CRM-UAM/CRMaze/Laberinto_OSHWDem/2016-10-10 19.41.19.jpg

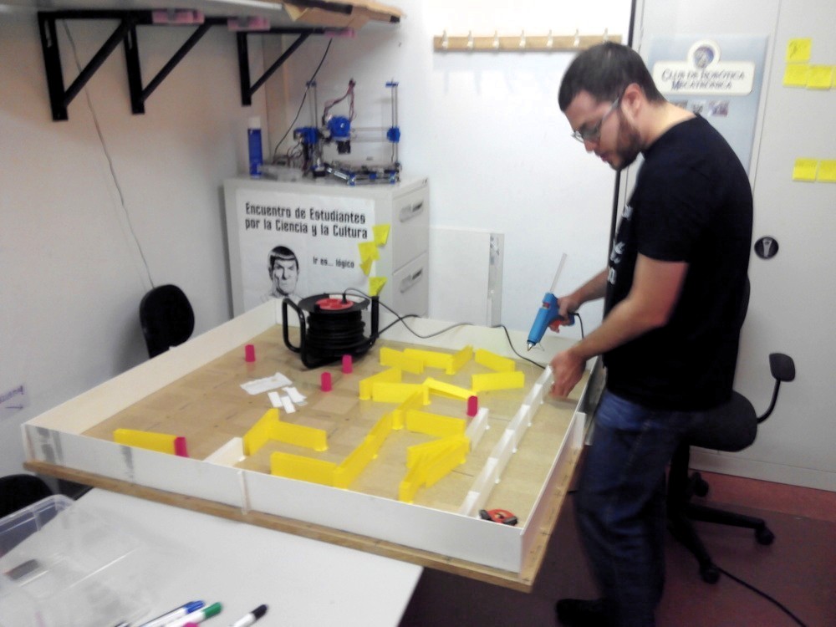
Laberinto_OSHWDem/2016-10-10 19.41.19.jpg
