CRM-UAM/CRMaze/Software/avr_lib_mpu6050_03/imu_arduino/imu_arduino.ino

#include <stdlib.h>
#include <avr/io.h>
#include <avr/interrupt.h>
#include <avr/pgmspace.h>
#include <util/delay.h>
#include <math.h>  //include libm

#include "mpu6050.h"

#define UART_BAUD_RATE 115200
#include "myuart.h"

int main(void) {

	#if MPU6050_GETATTITUDE == 0
    int16_t ax = 0;
    int16_t ay = 0;
    int16_t az = 0;
    int16_t gx = 0;
    int16_t gy = 0;
    int16_t gz = 0;
    double axg = 0;
    double ayg = 0;
    double azg = 0;
    double gxds = 0;
    double gyds = 0;
    double gzds = 0;
	#endif

	#if MPU6050_GETATTITUDE == 1 || MPU6050_GETATTITUDE == 2
    long *ptr = 0;
    double qw = 1.0f;
	double qx = 0.0f;
	double qy = 0.0f;
	double qz = 0.0f;
	double roll = 0.0f;
	double pitch = 0.0f;
	double yaw = 0.0f;
	#endif

    //init uart
	uart_init(UART_BAUD_SELECT(UART_BAUD_RATE,F_CPU));

	//init interrupt
	sei();

	//init mpu6050
	mpu6050_init();
	_delay_ms(50);

	//init mpu6050 dmp processor
	#if MPU6050_GETATTITUDE == 2
	mpu6050_dmpInitialize();
	mpu6050_dmpEnable();
	_delay_ms(10);
	#endif

	for(;;) {
		#if MPU6050_GETATTITUDE == 0
		mpu6050_getRawData(&ax, &ay, &az, &gx, &gy, &gz);
		mpu6050_getConvData(&axg, &ayg, &azg, &gxds, &gyds, &gzds);
		#endif

		#if MPU6050_GETATTITUDE == 1
		mpu6050_getQuaternion(&qw, &qx, &qy, &qz);
		mpu6050_getRollPitchYaw(&roll, &pitch, &yaw);
		_delay_ms(10);
		#endif

		#if MPU6050_GETATTITUDE == 2
		if(mpu6050_getQuaternionWait(&qw, &qx, &qy, &qz)) {
			mpu6050_getRollPitchYaw(qw, qx, qy, qz, &roll, &pitch, &yaw);
		}
		_delay_ms(10);
		#endif

		#if MPU6050_GETATTITUDE == 0
		char itmp[10];
		ltoa(ax, itmp, 10); uart_putc(' '); uart_puts(itmp); uart_putc(' ');
		ltoa(ay, itmp, 10); uart_putc(' '); uart_puts(itmp); uart_putc(' ');
		ltoa(az, itmp, 10); uart_putc(' '); uart_puts(itmp); uart_putc(' ');
		ltoa(gx, itmp, 10); uart_putc(' '); uart_puts(itmp); uart_putc(' ');
		ltoa(gy, itmp, 10); uart_putc(' '); uart_puts(itmp); uart_putc(' ');
		ltoa(gz, itmp, 10); uart_putc(' '); uart_puts(itmp); uart_putc(' ');
		uart_puts("\r\n");

		dtostrf(axg, 3, 5, itmp); uart_puts(itmp); uart_putc(' ');
		dtostrf(ayg, 3, 5, itmp); uart_puts(itmp); uart_putc(' ');
		dtostrf(azg, 3, 5, itmp); uart_puts(itmp); uart_putc(' ');
		dtostrf(gxds, 3, 5, itmp); uart_puts(itmp); uart_putc(' ');
		dtostrf(gyds, 3, 5, itmp); uart_puts(itmp); uart_putc(' ');
		dtostrf(gzds, 3, 5, itmp); uart_puts(itmp); uart_putc(' ');
		uart_puts("\r\n");

		uart_puts("\r\n");

		_delay_ms(1000);
		#endif

		#if MPU6050_GETATTITUDE == 1 || MPU6050_GETATTITUDE == 2

		//quaternion
		ptr = (long *)(&qw);
		uart_putc(*ptr);
		uart_putc(*ptr>>8);
		uart_putc(*ptr>>16);
		uart_putc(*ptr>>24);
		ptr = (long *)(&qx);
		uart_putc(*ptr);
		uart_putc(*ptr>>8);
		uart_putc(*ptr>>16);
		uart_putc(*ptr>>24);
		ptr = (long *)(&qy);
		uart_putc(*ptr);
		uart_putc(*ptr>>8);
		uart_putc(*ptr>>16);
		uart_putc(*ptr>>24);
		ptr = (long *)(&qz);
		uart_putc(*ptr);
		uart_putc(*ptr>>8);
		uart_putc(*ptr>>16);
		uart_putc(*ptr>>24);

		//roll pitch yaw
		ptr = (long *)(&roll);
		uart_putc(*ptr);
		uart_putc(*ptr>>8);
		uart_putc(*ptr>>16);
		uart_putc(*ptr>>24);
		ptr = (long *)(&pitch);
		uart_putc(*ptr);
		uart_putc(*ptr>>8);
		uart_putc(*ptr>>16);
		uart_putc(*ptr>>24);
		ptr = (long *)(&yaw);
		uart_putc(*ptr);
		uart_putc(*ptr>>8);
		uart_putc(*ptr>>16);
		uart_putc(*ptr>>24);

		uart_putc('\n');
		#endif

	}

}
