CRM-UAM/CRMaze/Software/avr_lib_mpu6050_03/imu_arduino/mpu6050.ino

/*
MPU6050 lib 0x02

copyright (c) Davide Gironi, 2012

Released under GPLv3.
Please refer to LICENSE file for licensing information.
*/


#include <stdlib.h>
#include <string.h>
#include <avr/io.h>
#include <avr/pgmspace.h>
#include <avr/interrupt.h>
#include <util/delay.h>

#include "mpu6050.h"

#if MPU6050_GETATTITUDE == 1 || MPU6050_GETATTITUDE == 2
#include <math.h>  //include libm
#endif

//path to i2c fleury lib
#include MPU6050_I2CFLEURYPATH

volatile uint8_t buffer[14];

/*
 * read bytes from chip register
 */
int8_t mpu6050_readBytes(uint8_t regAddr, uint8_t length, uint8_t *data) {
	uint8_t i = 0;
	int8_t count = 0;
	if(length > 0) {
		//request register
		i2c_start(MPU6050_ADDR | I2C_WRITE);
		i2c_write(regAddr);
		_delay_us(10);
		//read data
		i2c_start(MPU6050_ADDR | I2C_READ);
		for(i=0; i<length; i++) {
			count++;
			if(i==length-1)
				data[i] = i2c_readNak();
			else
				data[i] = i2c_readAck();
		}
		i2c_stop();
	}
	return count;
}

/*
 * read 1 byte from chip register
 */
int8_t mpu6050_readByte(uint8_t regAddr, uint8_t *data) {
    return mpu6050_readBytes(regAddr, 1, data);
}

/*
 * write bytes to chip register
 */
void mpu6050_writeBytes(uint8_t regAddr, uint8_t length, uint8_t* data) {
	if(length > 0) {
		//write data
		i2c_start(MPU6050_ADDR | I2C_WRITE);
		i2c_write(regAddr); //reg
    uint8_t i;
		for (i = 0; i < length; i++) {
			i2c_write((uint8_t) data[i]);
		}
		i2c_stop();
	}
}

/*
 * write 1 byte to chip register
 */
void mpu6050_writeByte(uint8_t regAddr, uint8_t data) {
    return mpu6050_writeBytes(regAddr, 1, &data);
}

/*
 * read bits from chip register
 */
int8_t mpu6050_readBits(uint8_t regAddr, uint8_t bitStart, uint8_t length, uint8_t *data) {
    // 01101001 read byte
    // 76543210 bit numbers
    //    xxx   args: bitStart=4, length=3
    //    010   masked
    //   -> 010 shifted
    int8_t count = 0;
    if(length > 0) {
		uint8_t b;
		if ((count = mpu6050_readByte(regAddr, &b)) != 0) {
			uint8_t mask = ((1 << length) - 1) << (bitStart - length + 1);
			b &= mask;
			b >>= (bitStart - length + 1);
			*data = b;
		}
    }
    return count;
}

/*
 * read 1 bit from chip register
 */
int8_t mpu6050_readBit(uint8_t regAddr, uint8_t bitNum, uint8_t *data) {
    uint8_t b;
    uint8_t count = mpu6050_readByte(regAddr, &b);
    *data = b & (1 << bitNum);
    return count;
}

/*
 * write bit/bits to chip register
 */
void mpu6050_writeBits(uint8_t regAddr, uint8_t bitStart, uint8_t length, uint8_t data) {
    //      010 value to write
    // 76543210 bit numbers
    //    xxx   args: bitStart=4, length=3
    // 00011100 mask byte
    // 10101111 original value (sample)
    // 10100011 original & ~mask
    // 10101011 masked | value
	if(length > 0) {
		uint8_t b = 0;
		if (mpu6050_readByte(regAddr, &b) != 0) { //get current data
			uint8_t mask = ((1 << length) - 1) << (bitStart - length + 1);
			data <<= (bitStart - length + 1); // shift data into correct position
			data &= mask; // zero all non-important bits in data
			b &= ~(mask); // zero all important bits in existing byte
			b |= data; // combine data with existing byte
			mpu6050_writeByte(regAddr, b);
		}
	}
}

/*
 * write one bit to chip register
 */
void mpu6050_writeBit(uint8_t regAddr, uint8_t bitNum, uint8_t data) {
    uint8_t b;
    mpu6050_readByte(regAddr, &b);
    b = (data != 0) ? (b | (1 << bitNum)) : (b & ~(1 << bitNum));
    mpu6050_writeByte(regAddr, b);
}

#if MPU6050_GETATTITUDE == 2
/*
 * write word/words to chip register
 */
void mpu6050_writeWords(uint8_t regAddr, uint8_t length, uint16_t* data) {
	if(length > 0) {
		uint8_t i = 0;
		//write data
		i2c_start(MPU6050_ADDR | I2C_WRITE);
		i2c_write(regAddr); //reg
		for (i = 0; i < length * 2; i++) {
			i2c_write((uint8_t)(data[i++] >> 8)); // send MSB
			i2c_write((uint8_t)data[i]);          // send LSB
		}
		i2c_stop();
	}
}

/*
 * set a chip memory bank
 */
void mpu6050_setMemoryBank(uint8_t bank, uint8_t prefetchEnabled, uint8_t userBank) {
    bank &= 0x1F;
    if (userBank) bank |= 0x20;
    if (prefetchEnabled) bank |= 0x40;
    mpu6050_writeByte(MPU6050_RA_BANK_SEL, bank);
}

/*
 * set memory start address
 */
void mpu6050_setMemoryStartAddress(uint8_t address) {
	mpu6050_writeByte(MPU6050_RA_MEM_START_ADDR, address);
}

/*
 * read a memory block
 */
void mpu6050_readMemoryBlock(uint8_t *data, uint16_t dataSize, uint8_t bank, uint8_t address) {
	mpu6050_setMemoryBank(bank, 0, 0);
	mpu6050_setMemoryStartAddress(address);
    uint8_t chunkSize;
    for (uint16_t i = 0; i < dataSize;) {
        // determine correct chunk size according to bank position and data size
        chunkSize = MPU6050_DMP_MEMORY_CHUNK_SIZE;

        // make sure we don't go past the data size
        if (i + chunkSize > dataSize) chunkSize = dataSize - i;

        // make sure this chunk doesn't go past the bank boundary (256 bytes)
        if (chunkSize > 256 - address) chunkSize = 256 - address;

        // read the chunk of data as specified
        mpu6050_readBytes(MPU6050_RA_MEM_R_W, chunkSize, data + i);

        // increase byte index by [chunkSize]
        i += chunkSize;

        // uint8_t automatically wraps to 0 at 256
        address += chunkSize;

        // if we aren't done, update bank (if necessary) and address
        if (i < dataSize) {
            if (address == 0) bank++;
            mpu6050_setMemoryBank(bank, 0, 0);
            mpu6050_setMemoryStartAddress(address);
        }
    }
}

/*
 * write a memory block
 */
uint8_t mpu6050_writeMemoryBlock(const uint8_t *data, uint16_t dataSize, uint8_t bank, uint8_t address, uint8_t verify, uint8_t useProgMem) {
	mpu6050_setMemoryBank(bank, 0, 0);
	mpu6050_setMemoryStartAddress(address);
    uint8_t chunkSize;
    uint8_t *verifyBuffer = 0;
    uint8_t *progBuffer = 0;
    uint16_t i;
    uint8_t j;
    if (verify) verifyBuffer = (uint8_t *)malloc(MPU6050_DMP_MEMORY_CHUNK_SIZE);
    if (useProgMem) progBuffer = (uint8_t *)malloc(MPU6050_DMP_MEMORY_CHUNK_SIZE);
    for (i = 0; i < dataSize;) {
        // determine correct chunk size according to bank position and data size
        chunkSize = MPU6050_DMP_MEMORY_CHUNK_SIZE;

        // make sure we don't go past the data size
        if (i + chunkSize > dataSize) chunkSize = dataSize - i;

        // make sure this chunk doesn't go past the bank boundary (256 bytes)
        if (chunkSize > 256 - address) chunkSize = 256 - address;

        if (useProgMem) {
            // write the chunk of data as specified
            for (j = 0; j < chunkSize; j++) progBuffer[j] = pgm_read_byte(data + i + j);
        } else {
            // write the chunk of data as specified
            progBuffer = (uint8_t *)data + i;
        }

        mpu6050_writeBytes(MPU6050_RA_MEM_R_W, chunkSize, progBuffer);

        // verify data if needed
        if (verify && verifyBuffer) {
        	mpu6050_setMemoryBank(bank, 0, 0);
            mpu6050_setMemoryStartAddress(address);
            mpu6050_readBytes(MPU6050_RA_MEM_R_W, chunkSize, verifyBuffer);
            if (memcmp(progBuffer, verifyBuffer, chunkSize) != 0) {
                free(verifyBuffer);
                if (useProgMem) free(progBuffer);
                return 0; // uh oh.
            }
        }

        // increase byte index by [chunkSize]
        i += chunkSize;

        // uint8_t automatically wraps to 0 at 256
        address += chunkSize;

        // if we aren't done, update bank (if necessary) and address
        if (i < dataSize) {
            if (address == 0) bank++;
            mpu6050_setMemoryBank(bank, 0, 0);
            mpu6050_setMemoryStartAddress(address);
        }
    }
    if (verify) free(verifyBuffer);
    if (useProgMem) free(progBuffer);
    return 1;
}

/*
 * write a dmp configuration set
 */
uint8_t mpu6050_writeDMPConfigurationSet(const uint8_t *data, uint16_t dataSize, uint8_t useProgMem) {
    uint8_t *progBuffer = 0;
    uint8_t success, special;
    uint16_t i, j;
    if (useProgMem) {
        progBuffer = (uint8_t *)malloc(8); // assume 8-byte blocks, realloc later if necessary
    }

    // config set data is a long string of blocks with the following structure:
    // [bank] [offset] [length] [byte[0], byte[1], ..., byte[length]]
    uint8_t bank, offset, length;
    for (i = 0; i < dataSize;) {
        if (useProgMem) {
            bank = pgm_read_byte(data + i++);
            offset = pgm_read_byte(data + i++);
            length = pgm_read_byte(data + i++);
        } else {
            bank = data[i++];
            offset = data[i++];
            length = data[i++];
        }

        // write data or perform special action
        if (length > 0) {
            // regular block of data to write
            if (useProgMem) {
                if (sizeof(progBuffer) < length) progBuffer = (uint8_t *)realloc(progBuffer, length);
                for (j = 0; j < length; j++) progBuffer[j] = pgm_read_byte(data + i + j);
            } else {
                progBuffer = (uint8_t *)data + i;
            }
            success = mpu6050_writeMemoryBlock(progBuffer, length, bank, offset, 1, 0);
            i += length;
        } else {
            // special instruction
            // NOTE: this kind of behavior (what and when to do certain things)
            // is totally undocumented. This code is in here based on observed
            // behavior only, and exactly why (or even whether) it has to be here
            // is anybody's guess for now.
            if (useProgMem) {
                special = pgm_read_byte(data + i++);
            } else {
                special = data[i++];
            }
            if (special == 0x01) {
                // enable DMP-related interrupts

            	//mpu6050_writeBit(MPU6050_RA_INT_ENABLE, MPU6050_INTERRUPT_ZMOT_BIT, 1); //setIntZeroMotionEnabled
            	//mpu6050_writeBit(MPU6050_RA_INT_ENABLE, MPU6050_INTERRUPT_FIFO_OFLOW_BIT, 1); //setIntFIFOBufferOverflowEnabled
            	//mpu6050_writeBit(MPU6050_RA_INT_ENABLE, MPU6050_INTERRUPT_DMP_INT_BIT, 1); //setIntDMPEnabled
            	mpu6050_writeByte(MPU6050_RA_INT_ENABLE, 0x32);  // single operation

                success = 1;
            } else {
                // unknown special command
                success = 0;
            }
        }

        if (!success) {
            if (useProgMem) free(progBuffer);
            return 0; // uh oh
        }
    }
    if (useProgMem) free(progBuffer);
    return 1;
}

/*
 * get the fifo count
 */
uint16_t mpu6050_getFIFOCount() {
	mpu6050_readBytes(MPU6050_RA_FIFO_COUNTH, 2, (uint8_t *)buffer);
    return (((uint16_t)buffer[0]) << 8) | buffer[1];
}

/*
 * read fifo bytes
 */
void mpu6050_getFIFOBytes(uint8_t *data, uint8_t length) {
	mpu6050_readBytes(MPU6050_RA_FIFO_R_W, length, data);
}

/*
 * get the interrupt status
 */
uint8_t mpu6050_getIntStatus() {
	mpu6050_readByte(MPU6050_RA_INT_STATUS, (uint8_t *)buffer);
    return buffer[0];
}

/*
 * reset fifo
 */
void mpu6050_resetFIFO() {
	mpu6050_writeBit(MPU6050_RA_USER_CTRL, MPU6050_USERCTRL_FIFO_RESET_BIT, 1);
}

/*
 * get gyro offset X
 */
int8_t mpu6050_getXGyroOffset() {
	mpu6050_readBits(MPU6050_RA_XG_OFFS_TC, MPU6050_TC_OFFSET_BIT, MPU6050_TC_OFFSET_LENGTH, (uint8_t *)buffer);
    return buffer[0];
}

/*
 * set gyro offset X
 */
void mpu6050_setXGyroOffset(int8_t offset) {
	mpu6050_writeBits(MPU6050_RA_XG_OFFS_TC, MPU6050_TC_OFFSET_BIT, MPU6050_TC_OFFSET_LENGTH, offset);
}

/*
 * get gyro offset Y
 */
int8_t mpu6050_getYGyroOffset() {
	mpu6050_readBits(MPU6050_RA_YG_OFFS_TC, MPU6050_TC_OFFSET_BIT, MPU6050_TC_OFFSET_LENGTH, (uint8_t *)buffer);
    return buffer[0];
}

/*
 * set gyro offset Y
 */
void mpu6050_setYGyroOffset(int8_t offset) {
	mpu6050_writeBits(MPU6050_RA_YG_OFFS_TC, MPU6050_TC_OFFSET_BIT, MPU6050_TC_OFFSET_LENGTH, offset);
}

/*
 * get gyro offset Z
 */
int8_t mpu6050_getZGyroOffset() {
	mpu6050_readBits(MPU6050_RA_ZG_OFFS_TC, MPU6050_TC_OFFSET_BIT, MPU6050_TC_OFFSET_LENGTH, (uint8_t *)buffer);
    return buffer[0];
}

/*
 * set gyro offset Z
 */
void mpu6050_setZGyroOffset(int8_t offset) {
	mpu6050_writeBits(MPU6050_RA_ZG_OFFS_TC, MPU6050_TC_OFFSET_BIT, MPU6050_TC_OFFSET_LENGTH, offset);
}
#endif

/*
 * set sleep disabled
 */
void mpu6050_setSleepDisabled() {
	mpu6050_writeBit(MPU6050_RA_PWR_MGMT_1, MPU6050_PWR1_SLEEP_BIT, 0);
}

/*
 * set sleep enabled
 */
void mpu6050_setSleepEnabled() {
	mpu6050_writeBit(MPU6050_RA_PWR_MGMT_1, MPU6050_PWR1_SLEEP_BIT, 1);
}


/*
 * test connectino to chip
 */
uint8_t mpu6050_testConnection() {
	mpu6050_readBits(MPU6050_RA_WHO_AM_I, MPU6050_WHO_AM_I_BIT, MPU6050_WHO_AM_I_LENGTH, (uint8_t *)buffer);
	if(buffer[0] == 0x34)
		return 1;
	else
		return 0;
}

/*
 * initialize the accel and gyro
 */
void mpu6050_init() {
	#if MPU6050_I2CINIT == 1
	//init i2c
	i2c_init();
	_delay_us(10);
	#endif

	//allow mpu6050 chip clocks to start up
	_delay_ms(100);

	//set sleep disabled
	mpu6050_setSleepDisabled();
	//wake up delay needed sleep disabled
	_delay_ms(10);

	//set clock source
	//  it is highly recommended that the device be configured to use one of the gyroscopes (or an external clock source)
	//  as the clock reference for improved stability
	mpu6050_writeBits(MPU6050_RA_PWR_MGMT_1, MPU6050_PWR1_CLKSEL_BIT, MPU6050_PWR1_CLKSEL_LENGTH, MPU6050_CLOCK_PLL_XGYRO);
	//set DLPF bandwidth to 42Hz
	mpu6050_writeBits(MPU6050_RA_CONFIG, MPU6050_CFG_DLPF_CFG_BIT, MPU6050_CFG_DLPF_CFG_LENGTH, MPU6050_DLPF_BW_42);
    //set sampe rate
	mpu6050_writeByte(MPU6050_RA_SMPLRT_DIV, 4); //1khz / (1 + 4) = 200Hz
	//set gyro range
	mpu6050_writeBits(MPU6050_RA_GYRO_CONFIG, MPU6050_GCONFIG_FS_SEL_BIT, MPU6050_GCONFIG_FS_SEL_LENGTH, MPU6050_GYRO_FS);
	//set accel range
	mpu6050_writeBits(MPU6050_RA_ACCEL_CONFIG, MPU6050_ACONFIG_AFS_SEL_BIT, MPU6050_ACONFIG_AFS_SEL_LENGTH, MPU6050_ACCEL_FS);

	#if MPU6050_GETATTITUDE == 1
	MPU6050_TIMER0INIT
	#endif
}

//can not accept many request if we alreay have getattitude requests
/*
 * get raw data
 */
void mpu6050_getRawData(int16_t* ax, int16_t* ay, int16_t* az, int16_t* gx, int16_t* gy, int16_t* gz) {
	mpu6050_readBytes(MPU6050_RA_ACCEL_XOUT_H, 14, (uint8_t *)buffer);

    *ax = (((int16_t)buffer[0]) << 8) | buffer[1];
    *ay = (((int16_t)buffer[2]) << 8) | buffer[3];
    *az = (((int16_t)buffer[4]) << 8) | buffer[5];
    *gx = (((int16_t)buffer[8]) << 8) | buffer[9];
    *gy = (((int16_t)buffer[10]) << 8) | buffer[11];
    *gz = (((int16_t)buffer[12]) << 8) | buffer[13];
}

/*
 * get raw data converted to g and deg/sec values
 */
void mpu6050_getConvData(double* axg, double* ayg, double* azg, double* gxds, double* gyds, double* gzds) {
	int16_t ax = 0;
	int16_t ay = 0;
	int16_t az = 0;
	int16_t gx = 0;
	int16_t gy = 0;
	int16_t gz = 0;
	mpu6050_getRawData(&ax, &ay, &az, &gx, &gy, &gz);

	#if MPU6050_CALIBRATEDACCGYRO == 1
    *axg = (double)(ax-MPU6050_AXOFFSET)/MPU6050_AXGAIN;
    *ayg = (double)(ay-MPU6050_AYOFFSET)/MPU6050_AYGAIN;
    *azg = (double)(az-MPU6050_AZOFFSET)/MPU6050_AZGAIN;
    *gxds = (double)(gx-MPU6050_GXOFFSET)/MPU6050_GXGAIN;
	*gyds = (double)(gy-MPU6050_GYOFFSET)/MPU6050_GYGAIN;
	*gzds = (double)(gz-MPU6050_GZOFFSET)/MPU6050_GZGAIN;
	#else
    *axg = (double)(ax)/MPU6050_AGAIN;
    *ayg = (double)(ay)/MPU6050_AGAIN;
    *azg = (double)(az)/MPU6050_AGAIN;
    *gxds = (double)(gx)/MPU6050_GGAIN;
	*gyds = (double)(gy)/MPU6050_GGAIN;
	*gzds = (double)(gz)/MPU6050_GGAIN;
	#endif
}

#if MPU6050_GETATTITUDE == 1

volatile float q0 = 1.0f, q1 = 0.0f, q2 = 0.0f, q3 = 0.0f;
volatile float integralFBx = 0.0f,  integralFBy = 0.0f, integralFBz = 0.0f;
/*
 * Mahony update function (for 6DOF)
 */
void mpu6050_mahonyUpdate(float gx, float gy, float gz, float ax, float ay, float az) {
	float norm;
	float halfvx, halfvy, halfvz;
	float halfex, halfey, halfez;
	float qa, qb, qc;

	// Compute feedback only if accelerometer measurement valid (avoids NaN in accelerometer normalisation)
	if(!((ax == 0.0f) && (ay == 0.0f) && (az == 0.0f))) {

		// Normalise accelerometer measurement
		norm = sqrt(ax * ax + ay * ay + az * az);
		ax /= norm;
		ay /= norm;
		az /= norm;

		// Estimated direction of gravity and vector perpendicular to magnetic flux
		halfvx = q1 * q3 - q0 * q2;
		halfvy = q0 * q1 + q2 * q3;
		halfvz = q0 * q0 - 0.5f + q3 * q3;

		// Error is sum of cross product between estimated and measured direction of gravity
		halfex = (ay * halfvz - az * halfvy);
		halfey = (az * halfvx - ax * halfvz);
		halfez = (ax * halfvy - ay * halfvx);

		// Compute and apply integral feedback if enabled
		if(mpu6050_mahonytwoKiDef > 0.0f) {
			integralFBx += mpu6050_mahonytwoKiDef * halfex * (1.0f / mpu6050_mahonysampleFreq);	// integral error scaled by Ki
			integralFBy += mpu6050_mahonytwoKiDef * halfey * (1.0f / mpu6050_mahonysampleFreq);
			integralFBz += mpu6050_mahonytwoKiDef * halfez * (1.0f / mpu6050_mahonysampleFreq);
			gx += integralFBx;	// apply integral feedback
			gy += integralFBy;
			gz += integralFBz;
		} else {
			integralFBx = 0.0f;	// prevent integral windup
			integralFBy = 0.0f;
			integralFBz = 0.0f;
		}

		// Apply proportional feedback
		gx += mpu6050_mahonytwoKpDef * halfex;
		gy += mpu6050_mahonytwoKpDef * halfey;
		gz += mpu6050_mahonytwoKpDef * halfez;
	}

	// Integrate rate of change of quaternion
	gx *= (0.5f * (1.0f / mpu6050_mahonysampleFreq));		// pre-multiply common factors
	gy *= (0.5f * (1.0f / mpu6050_mahonysampleFreq));
	gz *= (0.5f * (1.0f / mpu6050_mahonysampleFreq));
	qa = q0;
	qb = q1;
	qc = q2;
	q0 += (-qb * gx - qc * gy - q3 * gz);
	q1 += (qa * gx + qc * gz - q3 * gy);
	q2 += (qa * gy - qb * gz + q3 * gx);
	q3 += (qa * gz + qb * gy - qc * gx);

	// Normalise quaternion
	norm = sqrt(q0 * q0 + q1 * q1 + q2 * q2 + q3 * q3);
	q0 /= norm;
	q1 /= norm;
	q2 /= norm;
	q3 /= norm;
}

/*
 * update quaternion
 */
void mpu6050_updateQuaternion() {
	int16_t ax = 0;
	int16_t ay = 0;
	int16_t az = 0;
	int16_t gx = 0;
	int16_t gy = 0;
	int16_t gz = 0;
	double axg = 0;
	double ayg = 0;
	double azg = 0;
	double gxrs = 0;
	double gyrs = 0;
	double gzrs = 0;

	//get raw data
	while(1) {
		mpu6050_readBit(MPU6050_RA_INT_STATUS, MPU6050_INTERRUPT_DATA_RDY_BIT, (uint8_t *)buffer);
		if(buffer[0])
			break;
		_delay_us(10);
	}

	mpu6050_readBytes(MPU6050_RA_ACCEL_XOUT_H, 14, (uint8_t *)buffer);
    ax = (((int16_t)buffer[0]) << 8) | buffer[1];
    ay = (((int16_t)buffer[2]) << 8) | buffer[3];
    az = (((int16_t)buffer[4]) << 8) | buffer[5];
    gx = (((int16_t)buffer[8]) << 8) | buffer[9];
    gy = (((int16_t)buffer[10]) << 8) | buffer[11];
    gz = (((int16_t)buffer[12]) << 8) | buffer[13];

	#if MPU6050_CALIBRATEDACCGYRO == 1
	axg = (double)(ax-MPU6050_AXOFFSET)/MPU6050_AXGAIN;
	ayg = (double)(ay-MPU6050_AYOFFSET)/MPU6050_AYGAIN;
	azg = (double)(az-MPU6050_AZOFFSET)/MPU6050_AZGAIN;
	gxrs = (double)(gx-MPU6050_GXOFFSET)/MPU6050_GXGAIN*0.01745329; //degree to radians
	gyrs = (double)(gy-MPU6050_GYOFFSET)/MPU6050_GYGAIN*0.01745329; //degree to radians
	gzrs = (double)(gz-MPU6050_GZOFFSET)/MPU6050_GZGAIN*0.01745329; //degree to radians
	#else
	axg = (double)(ax)/MPU6050_AGAIN;
	ayg = (double)(ay)/MPU6050_AGAIN;
	azg = (double)(az)/MPU6050_AGAIN;
	gxrs = (double)(gx)/MPU6050_GGAIN*0.01745329; //degree to radians
	gyrs = (double)(gy)/MPU6050_GGAIN*0.01745329; //degree to radians
	gzrs = (double)(gz)/MPU6050_GGAIN*0.01745329; //degree to radians
	#endif

    //compute data
    mpu6050_mahonyUpdate(gxrs, gyrs, gzrs, axg, ayg, azg);
}

/*
 * update timer for attitude
 */
ISR(TIMER0_OVF_vect) {
	mpu6050_updateQuaternion();
}

/*
 * get quaternion
 */
void mpu6050_getQuaternion(double *qw, double *qx, double *qy, double *qz) {
	*qw = q0;
	*qx = q1;
	*qy = q2;
	*qz = q3;
}

/*
 * get euler angles
 * aerospace sequence, to obtain sensor attitude:
 * 1. rotate around sensor Z plane by yaw
 * 2. rotate around sensor Y plane by pitch
 * 3. rotate around sensor X plane by roll
 */
void mpu6050_getRollPitchYaw(double *roll, double *pitch, double *yaw) {
	*yaw = atan2(2*q1*q2 - 2*q0*q3, 2*q0*q0 + 2*q1*q1 - 1);
	*pitch = -asin(2*q1*q3 + 2*q0*q2);
	*roll = atan2(2*q2*q3 - 2*q0*q1, 2*q0*q0 + 2*q3*q3 - 1);
}

#endif
